drakarah/double-bass-pre-amplifier/LTSpiceSchematic/preamp.asc

B1: bi; I = (V(VCC) * I(Vbatt)) / (3.7 * 0.85)
Cbass: cap; 100nf
Cbias: cap; 10µF
CdecoupleHF1: cap; 100nF; Rser=50m
CdecoupleHF: cap; 100nF; Rser=50m
CdecoupleLF: cap; 10µF; Rser=1
Chpf: cap; 100nF
Cin: cap; 100nF
Cout: cap; 1µF
Cpickup: cap; 10nF
Ctreble: cap; 47nF
Dprotect1: diode; 1N4148
Dprotect2: diode; 1N4148
Rbass_fb: res; 4.7k
Rbass_in: res; 4.7k
Rbias_bottom: res; 100k
Rbias_top: res; 100k
Rgain: res; 3.3k
Rhpf_bias: res; 56k
Rin: res; 10Mega
Rload: res; 10k
Rout_pulldown: res; 100k
RoutIsolation: res; 100
RpotBass: pot; Rtot=10K wiper=0.5
RpotGain: pot; Rtot=10K wiper=1
RpotTreble: pot; Rtot=10K wiper=0.5
Rprotect: res; 1k
Rtreble_fb: res; 10k
Rtreble_in: res; 10k
Rtreble_s1: res; 2.2k
Rtreble_s2: res; 2.2k
U1: OPAx134
U2: OPAx134
U3: OPAx134
U4: OPAx134
V_lipo: battery; 3.7
Vbatt: voltage; 9; Rser=1
Vpickup: voltage; PWL file=pluck_11k.txt; AC 1
Named nets: 0, LINE_OUT, PREAMP_OUT, VBIAS, PICKUP, FILTER_OUT, VCC, TREBLE_OUT, BASS_OUT, BATTERY
.inc .\\lib\\sub\\OPAx134.LIB
;.tran 0 1000m 0
.ac dec 100 1 100k
;.op
.options reltol=0.003
.options method=gear
.wave simulated.wav 32 44100 V(LINE_OUT)
.inc .\\lib\\sub\\pot.sub
.meas tran VinMax MAX V(N002) FROM 1m TO 20m
.meas tran VinMin MIN V(N002) FROM 1m TO 20m
.meas tran VoutMax MAX V(FILTER_OUT) FROM 1m TO 20m
.meas tran VoutMin MIN V(FILTER_OUT) FROM 1m TO 20m
.meas tran Gain PARAM='(VoutMax-VoutMin)/(VinMax-VinMin)'
 
.meas tran T_settle WHEN V(VBIAS) = 4.41
Treble stage
Gain stage
Buffer stage
High pass filter
Bass stage
